ukmaker/VideoTrigger/images/IMG_0901.JPG

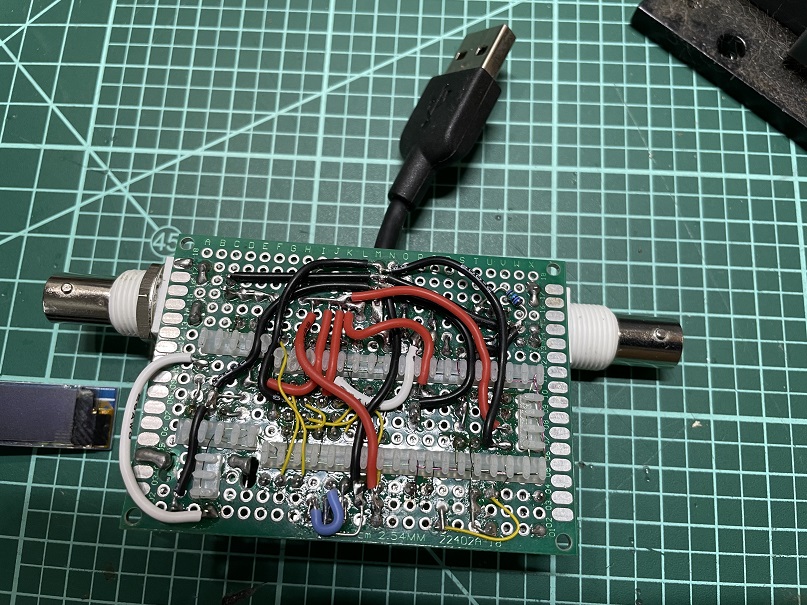
images/IMG_0901.JPG
