ukmaker/VideoTrigger/images/IMG_0900.JPG

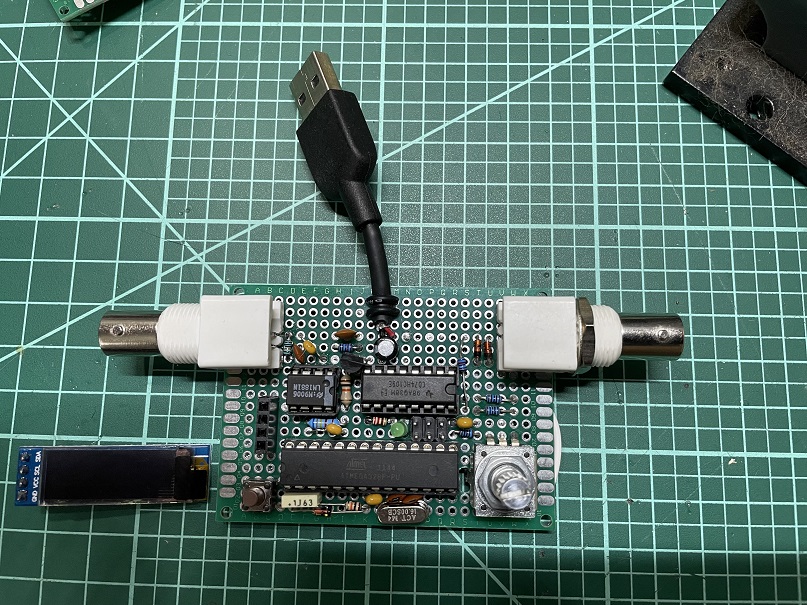
images/IMG_0900.JPG
